rodriguezhh/IA_SIDIEN/Software/Interfaz/told2_v0.1/detections/2023-04-19 22:40:39.263802.JPG

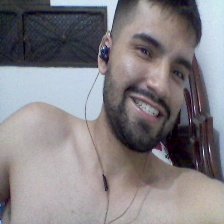
Software/Interfaz/told2_v0.1/detections/2023-04-19 22:40:39.263802.JPG
