rodriguezhh/IA_SIDIEN/Software/Interfaz/pruebas_de_rendimiento/parejas_early/parejas_early/2023-04-05 05_23_15.101974.JPG

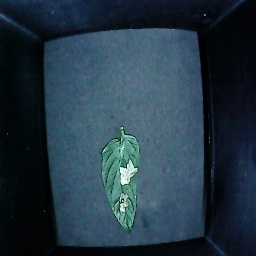
Software/Interfaz/pruebas_de_rendimiento/parejas_early/parejas_early/2023-04-05 05_23_15.101974.JPG
