rodriguezhh/IA_SIDIEN/Software/Interfaz/pruebas_de_rendimiento/parejas_early/parejas_early/2023-04-05 05_25_07.543546.JPG

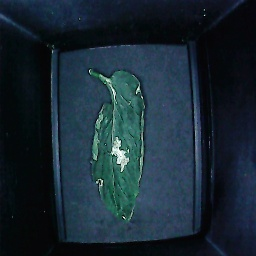
Software/Interfaz/pruebas_de_rendimiento/parejas_early/parejas_early/2023-04-05 05_25_07.543546.JPG
