rodriguezhh/IA_SIDIEN/Software/Interfaz/pruebas_de_rendimiento/parejas_early/parejas_early/2023-04-05 05_26_44.443964.JPG

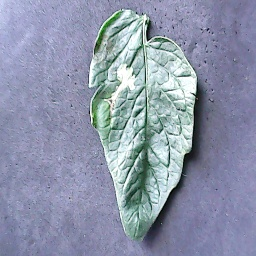
Software/Interfaz/pruebas_de_rendimiento/parejas_early/parejas_early/2023-04-05 05_26_44.443964.JPG
