rodriguezhh/IA_SIDIEN/Software/Interfaz/pruebas_de_rendimiento/parejas_healthy/parejas_healthy/2023-03-28 23_33_12.660300.JPG

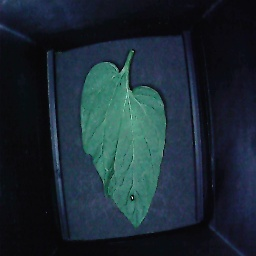
Software/Interfaz/pruebas_de_rendimiento/parejas_healthy/parejas_healthy/2023-03-28 23_33_12.660300.JPG
