rodriguezhh/IA_SIDIEN/Software/Interfaz/pruebas_de_rendimiento/parejas_late/parejas_late/2023-03-29 00_11_28.551215.JPG

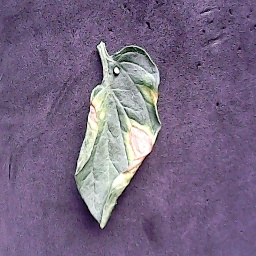
Software/Interfaz/pruebas_de_rendimiento/parejas_late/parejas_late/2023-03-29 00_11_28.551215.JPG
