rodriguezhh/IA_SIDIEN/Software/Interfaz/pruebas_de_rendimiento/parejas_late/parejas_late/2023-03-29 00_12_50.197784.JPG

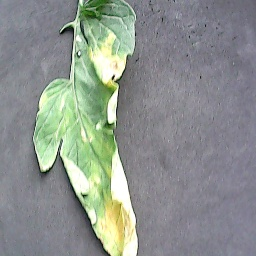
Software/Interfaz/pruebas_de_rendimiento/parejas_late/parejas_late/2023-03-29 00_12_50.197784.JPG
