rodriguezhh/IA_SIDIEN/Software/Interfaz/pruebas_de_rendimiento/parejas_late/parejas_late/2023-03-29 00_13_30.492437.JPG

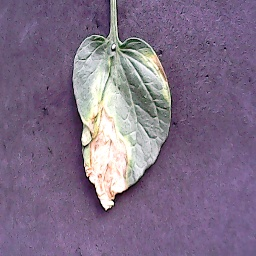
Software/Interfaz/pruebas_de_rendimiento/parejas_late/parejas_late/2023-03-29 00_13_30.492437.JPG
