rodriguezhh/IA_SIDIEN/Software/Interfaz/pruebas_de_rendimiento/parejas_mosaico/2023-04-05 05_23_23.629482.JPG

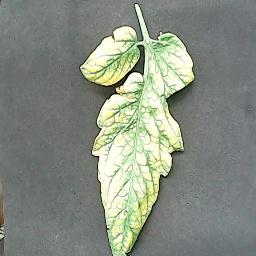
Software/Interfaz/pruebas_de_rendimiento/parejas_mosaico/2023-04-05 05_23_23.629482.JPG
