rodriguezhh/IA_SIDIEN/Software/Interfaz/pruebas_de_rendimiento/parejas_mosaico/2023-04-05 05_35_32.221255.JPG

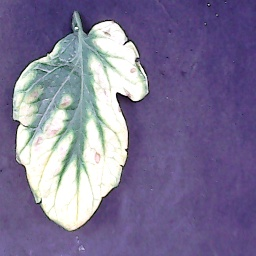
Software/Interfaz/pruebas_de_rendimiento/parejas_mosaico/2023-04-05 05_35_32.221255.JPG
