rodriguezhh/IA_SIDIEN/Software/Interfaz/pruebas_de_rendimiento/parejas_mosaico/2023-04-05 05_36_34.519450.JPG

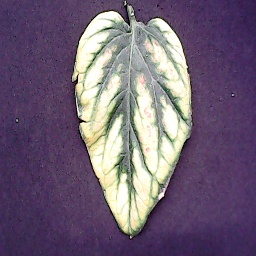
Software/Interfaz/pruebas_de_rendimiento/parejas_mosaico/2023-04-05 05_36_34.519450.JPG
