rodriguezhh/IA_SIDIEN/Software/Interfaz/pruebas_de_rendimiento/parejas_mosaico/2023-04-05 05_42_20.911598.JPG

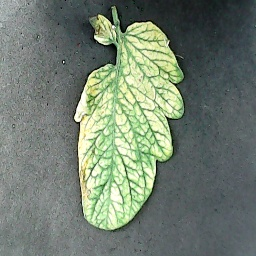
Software/Interfaz/pruebas_de_rendimiento/parejas_mosaico/2023-04-05 05_42_20.911598.JPG
