rodriguezhh/IA_SIDIEN/Software/Interfaz/pruebas_de_rendimiento/parejas_mosaico/2023-04-05 06_02_23.786281.JPG

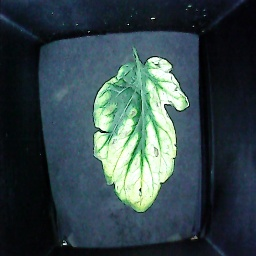
Software/Interfaz/pruebas_de_rendimiento/parejas_mosaico/2023-04-05 06_02_23.786281.JPG
