rodriguezhh/IA_SIDIEN/Software/Interfaz/pruebas_de_rendimiento/parejas_mosaico/2023-04-05 06_15_40.679586.JPG

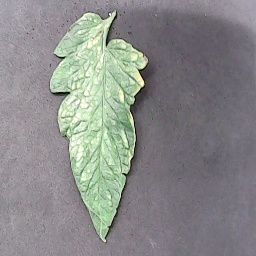
Software/Interfaz/pruebas_de_rendimiento/parejas_mosaico/2023-04-05 06_15_40.679586.JPG
