rodriguezhh/IA_SIDIEN/Software/Interfaz/pruebas_de_rendimiento/parejas_mosaico/2023-04-05 06_21_44.987504.JPG

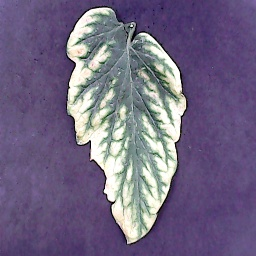
Software/Interfaz/pruebas_de_rendimiento/parejas_mosaico/2023-04-05 06_21_44.987504.JPG
