rodriguezhh/IA_SIDIEN/Software/Interfaz/pruebas_de_rendimiento/parejas_mosaico/2023-04-05 06_22_39.801959.JPG

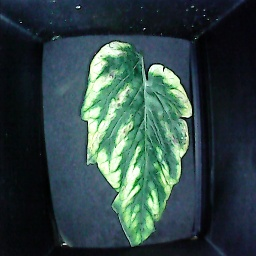
Software/Interfaz/pruebas_de_rendimiento/parejas_mosaico/2023-04-05 06_22_39.801959.JPG
