rodriguezhh/IA_SIDIEN/Hardware/PCB_leds/pads.pdf

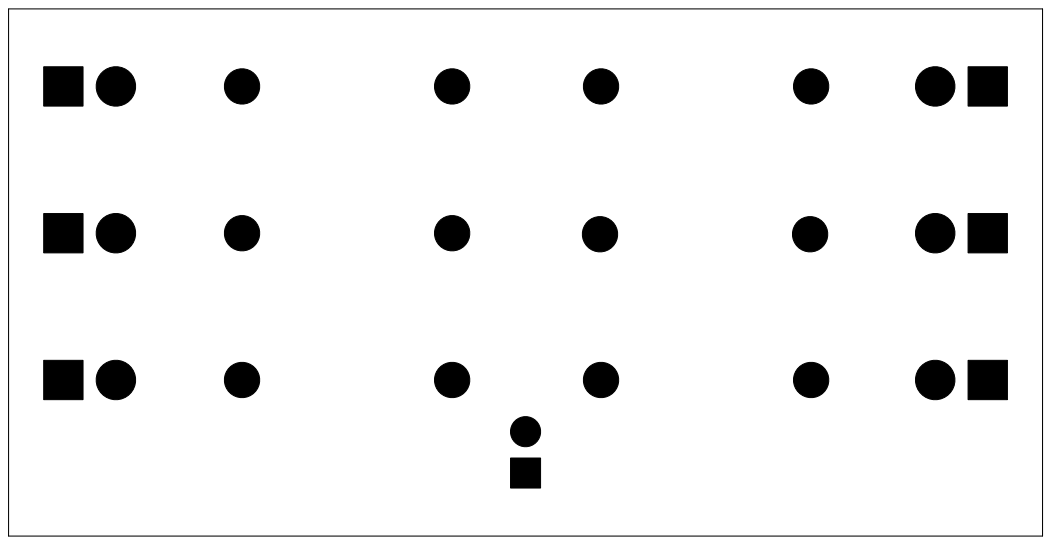
[picture p75: page 1]
