rodriguezhh/IA_SIDIEN/Hardware/PCB_leds/silk_frontal.pdf

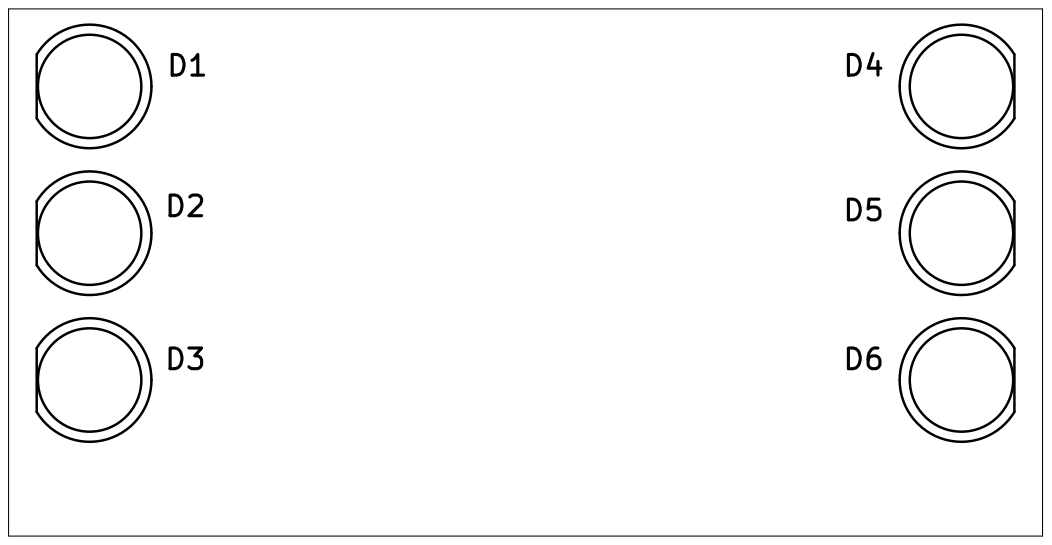
[picture p76: page 1]
