rodriguezhh/IA_SIDIEN/Hardware/PCB_leds/silk_trasero.pdf

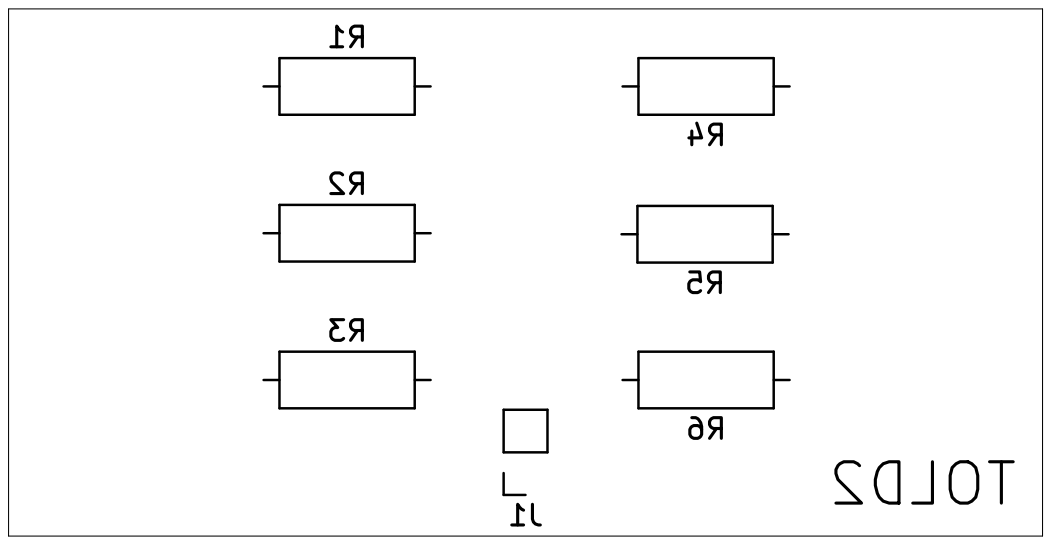
[picture p77: page 1]
