rodriguezhh/IA_SIDIEN/Hardware/PCB_leds/superior.pdf

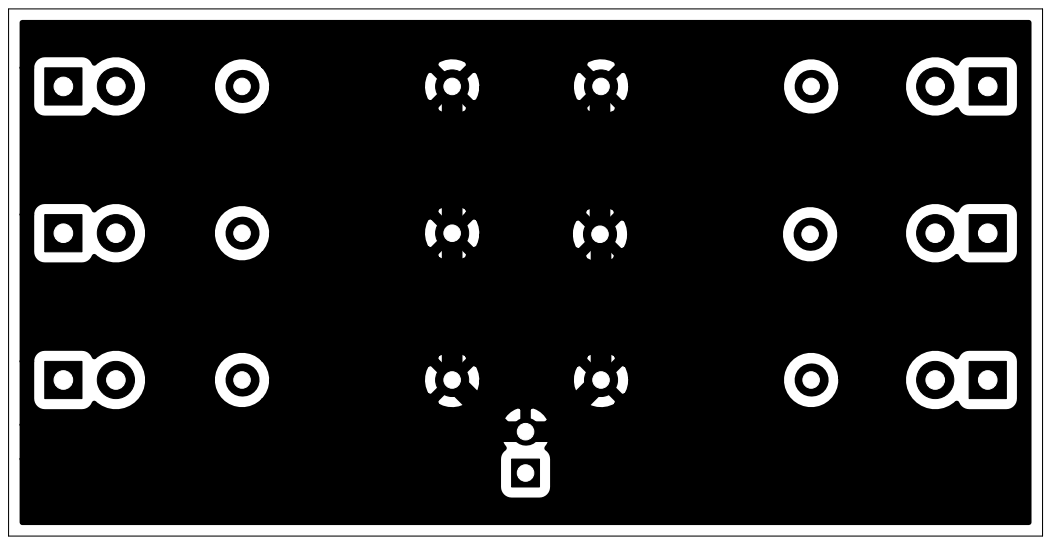
[picture p78: page 1]
